AteamVentures/CREATABLE_D3/Hardware/MainBoard/2nd/MAINBOARD_02_20181023_GERBER/nc_param.txt

INTEGER-PLACES         3
DECIMAL-PLACES         5
X-OFFSET               0.000000
Y-OFFSET               0.000000
FEEDRATE               1
COORDINATES            ABSOLUTE
OUTPUT-UNITS           METRIC
TOOL-ORDER             INCREASING
REPEAT-CODES           YES
SUPPRESS-LEAD-ZEROES   NO
SUPPRESS-TRAIL-ZEROES  NO
SUPPRESS-EQUAL         NO
TOOL-SELECT            NO
OPTIMIZE_DRILLING      NO
ENHANCED_EXCELLON      NO
HEADER                 none
LEADER                 12
CODE                   ASCII
SEPARATE               NO
SEPARATE-ROUTING       NO
DRILLING               LAYER-PAIR
BACKDRILL              NO
COUNTER                NO
CAVITY                 NO
TOLERANCE_DRILL        NO
TOLERANCE_TRAVEL       NO
TOOL_SIZE              NO
ROTATION               NO
NON_STANDARD           NO
TOTAL_DRILL            YES
SEPARATE_SLOT          NO
SUPPRESS_TOLERANCE     YES
SUPPRESS_TOOLSIZE      YES
SUPPRESS_ROTATION      YES
