AteamVentures/CREATABLE_D3/Hardware/MainBoard/1st/gerber/art_param.txt

DEVICE-TYPE           GERBER6X00
OUTPUT-UNITS          INCHES
FILM-SIZE             24000 16000
FORMAT                5.3
ABORT-ON-ERROR        NO
SCALE                 1
G-CODES               NO
OPTIMIZE              YES
STATIONS-PER-WHEEL    999
COORDINATES           ABSOLUTE
SUPPRESS-LEAD-ZEROES  YES
SUPPRESS-TRAIL-ZEROES NO
SUPPRESS-EQUAL        YES
